satorusaka/15k-macropad/Source/marbastlib/3d/CON_TYPE-C-31-M-14.step

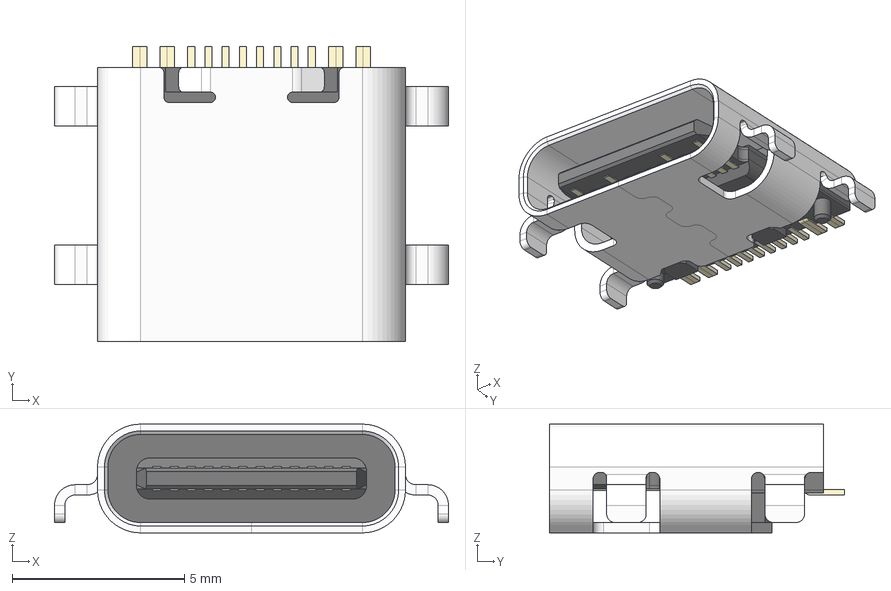
[picture p19: CAD file, 2022-09-09]
Source/marbastlib/3d/CON_TYPE-C-31-M-14.step
11.5 x 8.56 x 3.16 mm
Shroud
Plastic Body & Connector
