satorusaka/15k-macropad/Source/marbastlib/3d/CON_SM06B-SRSS-TB.step

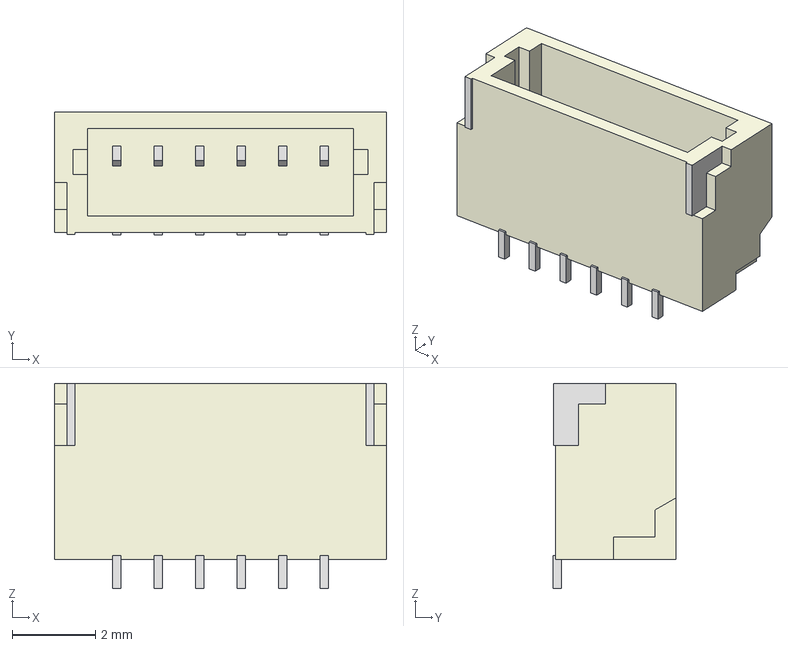
[picture p20: CAD file, 2022-09-09]
Source/marbastlib/3d/CON_SM06B-SRSS-TB.step
8.00 x 2.96 x 4.95 mm
