satorusaka/15k-macropad/Source/marbastlib/3d/Switch_ESP3020.step

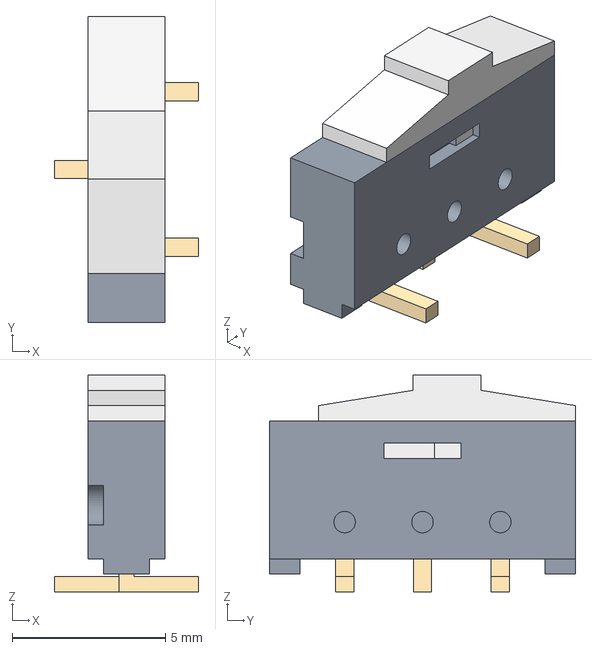
[picture p21: CAD file, 2022-09-09]
Source/marbastlib/3d/Switch_ESP3020.step
4.70 x 10.0 x 7.08 mm
