satorusaka/15k-macropad/Source/marbastlib/3d/LED_WS2812_2020.step

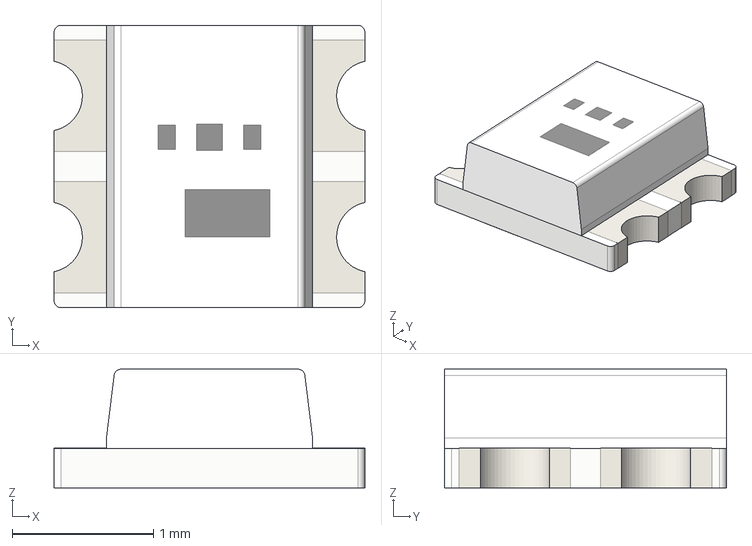
[picture p22: CAD file, 2022-09-09]
Source/marbastlib/3d/LED_WS2812_2020.step
2.20 x 2.00 x 0.842 mm
