satorusaka/15k-macropad/Source/marbastlib/3d/CON_SM05B-SRSS-TB.step

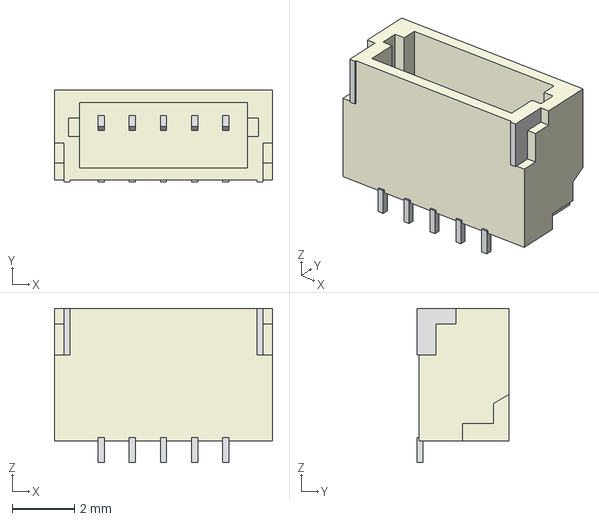
[picture p23: CAD file, 2022-09-09]
Source/marbastlib/3d/CON_SM05B-SRSS-TB.step
7.00 x 2.96 x 4.95 mm
