satorusaka/15k-macropad/Source/marbastlib/3d/CON_SM04B-SRSS-TB.step

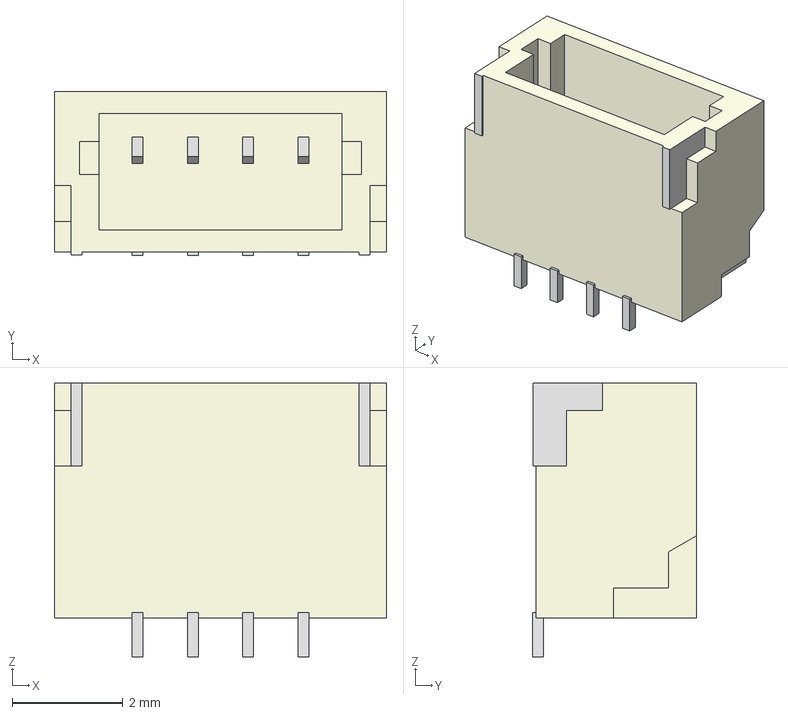
[picture p25: CAD file, 2022-09-09]
Source/marbastlib/3d/CON_SM04B-SRSS-TB.step
6.00 x 2.96 x 4.95 mm
