satorusaka/15k-macropad/Source/marbastlib/3d/Crystal_FA-128.step

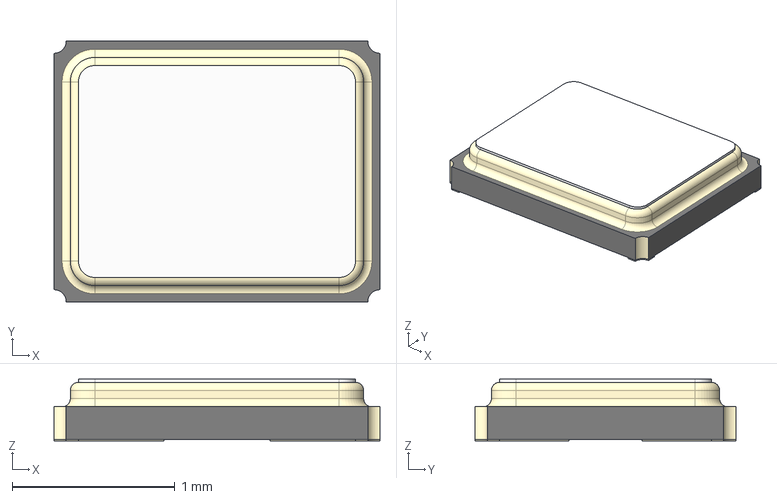
[picture p26: CAD file, 2022-09-09]
Source/marbastlib/3d/Crystal_FA-128.step
2.00 x 1.60 x 0.38 mm
