satorusaka/15k-macropad/Source/marbastlib/3d/ROT_EC11N.step

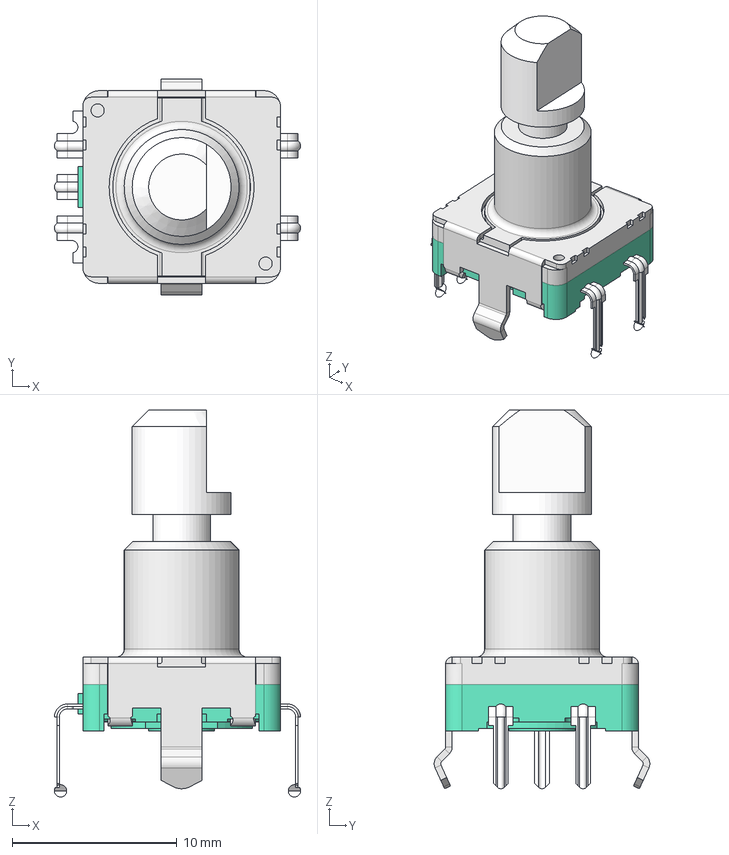
[picture p27: CAD file, 2022-09-09]
Source/marbastlib/3d/ROT_EC11N.step
14.9 x 13.1 x 23.5 mm
