satorusaka/15k-macropad/Source/marbastlib/3d/joystick_psp1000.step

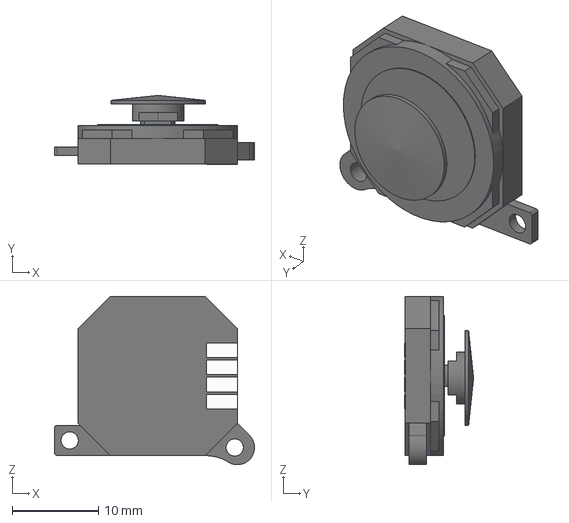
[picture p28: CAD file, 2022-09-09]
Source/marbastlib/3d/joystick_psp1000.step
23.2 x 8.05 x 19.6 mm
