satorusaka/15k-macropad/Source/marbastlib/3d/CON_MJ-4PP-9.step

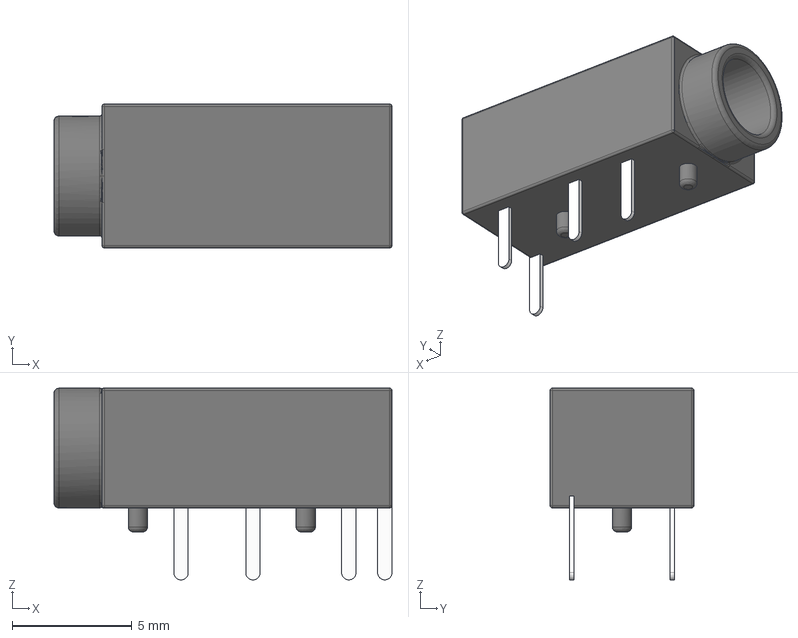
[picture p29: CAD file, 2022-09-09]
Source/marbastlib/3d/CON_MJ-4PP-9.step
14.1 x 6.00 x 8.00 mm
