satorusaka/15k-macropad/Source/marbastlib/3d/SW_SSSS213100.step

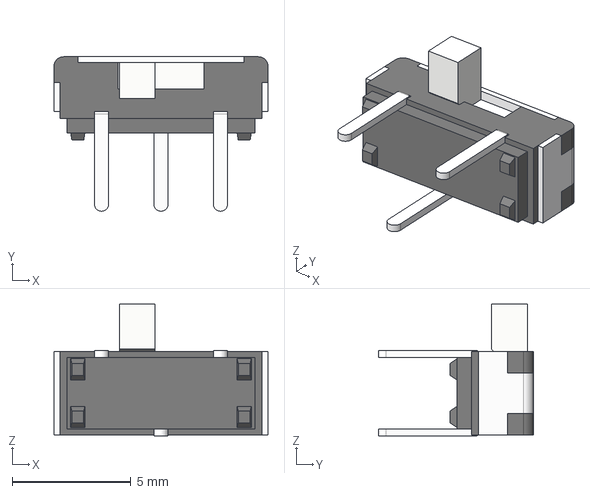
[picture p30: CAD file, 2022-09-09]
Source/marbastlib/3d/SW_SSSS213100.step
9.00 x 6.50 x 5.55 mm
