satorusaka/15k-macropad/Source/marbastlib/3d/CON_TYPE-C-31-M-12.step

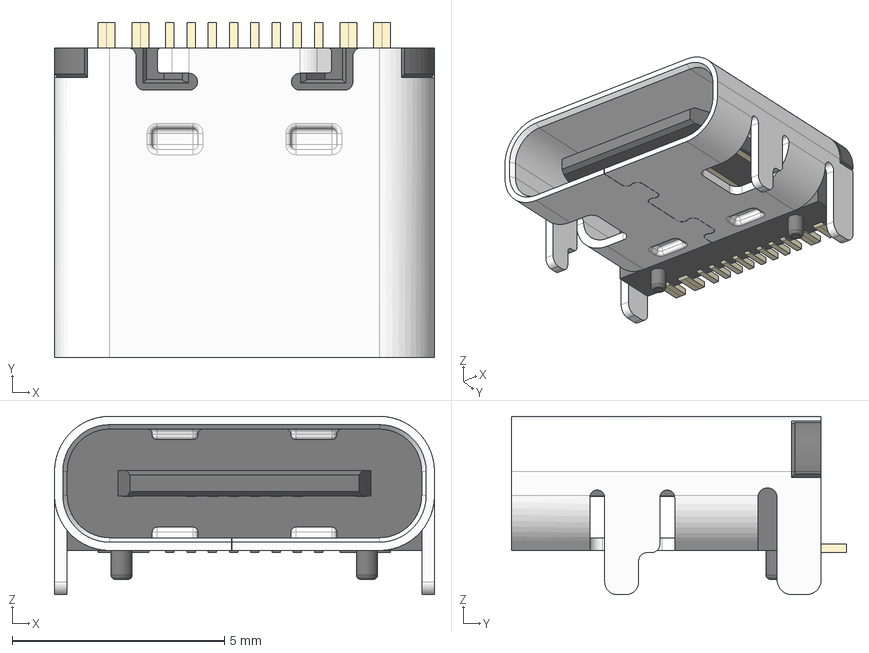
[picture p31: CAD file, 2022-09-09]
Source/marbastlib/3d/CON_TYPE-C-31-M-12.step
8.95 x 7.90 x 4.20 mm
ConPins
PcbPins
Mold
Frame
