satorusaka/15k-macropad/Source/marbastlib/3d/LED_WS2812B-MINI.step

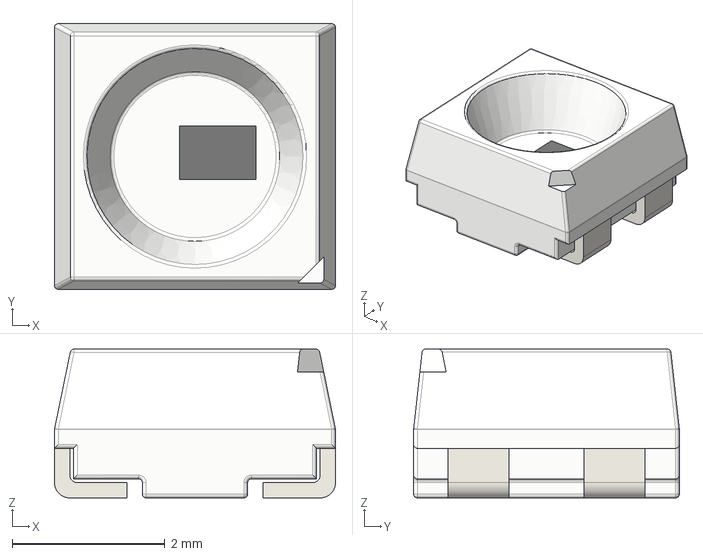
[picture p32: CAD file, 2022-09-09]
Source/marbastlib/3d/LED_WS2812B-MINI.step
3.68 x 3.48 x 1.95 mm
