satorusaka/15k-macropad/Source/marbastlib/3d/HS_Kailh_MX.step

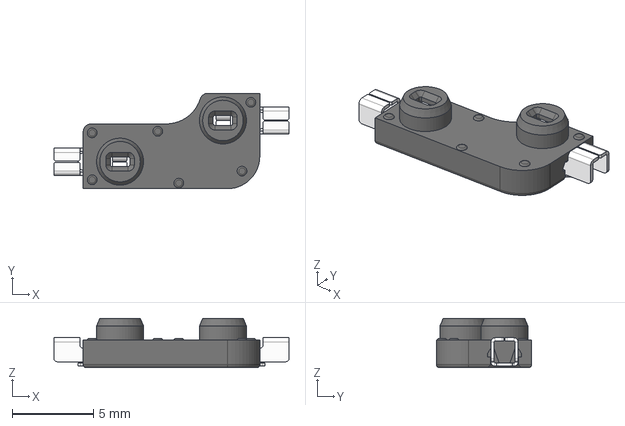
[picture p33: CAD file, 2022-09-09]
Source/marbastlib/3d/HS_Kailh_MX.step
14.5 x 5.89 x 3.05 mm
Contact x 2
