satorusaka/15k-macropad/Source/marbastlib/3d/HS_Kailh_Choc.step

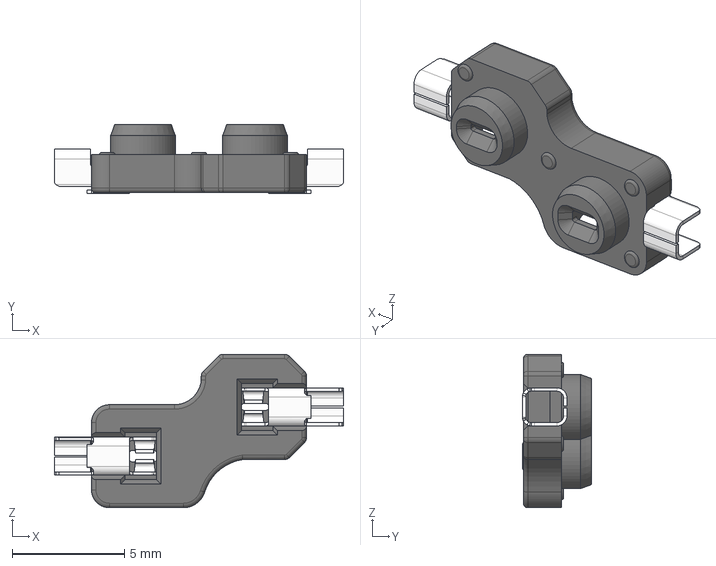
[picture p34: CAD file, 2022-09-09]
Source/marbastlib/3d/HS_Kailh_Choc.step
12.9 x 3.09 x 6.85 mm
pin x 2
socket
